telzo2000/cool942tb/case_design/stl/magent_bottomcase/cool942tb_magnet_right_bottomcase.step

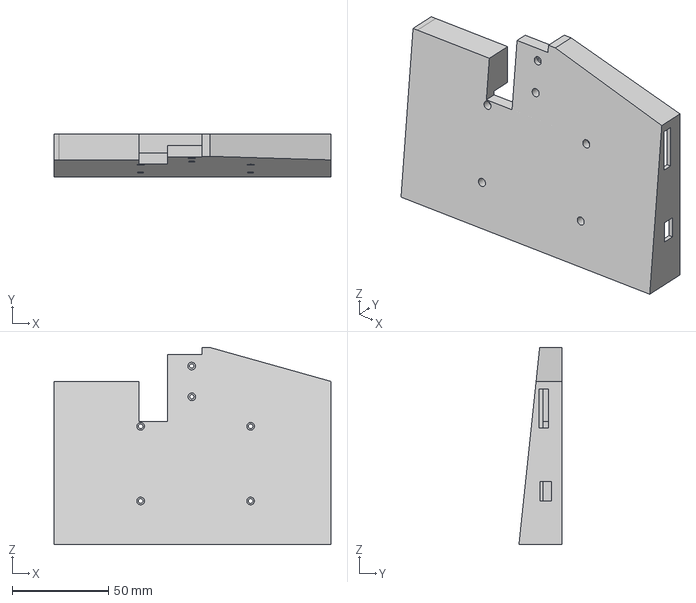
[picture p18: CAD file, 2025-01-30]
case_design/stl/magent_bottomcase/cool942tb_magnet_right_bottomcase.step
144.0 x 22.4 x 102.4 mm
