telzo2000/cool942tb/case_design/stl/with_battery_bottomcase/cool942tb_right_with_battery_bottomcase_6mm.stl

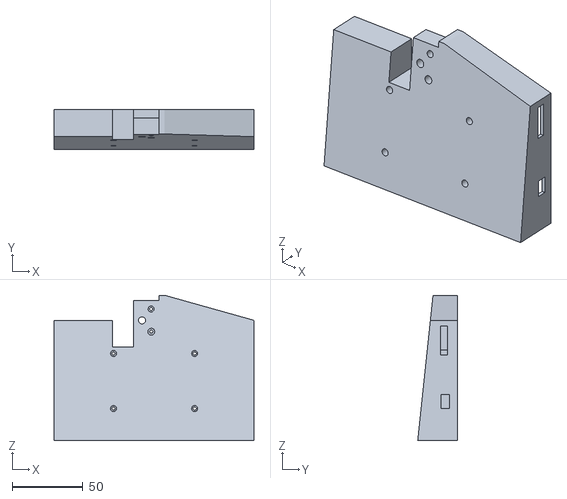
[picture p19: CAD file, 2025-02-10]
case_design/stl/with_battery_bottomcase/cool942tb_right_with_battery_bottomcase_6mm.stl
140.8 x 27.9 x 102.4
