telzo2000/cool942tb/case_design/stl/with_Battery_bottomcase_and_magnet/cool942tb_left_with_battery_bottomcase_6mm.stl

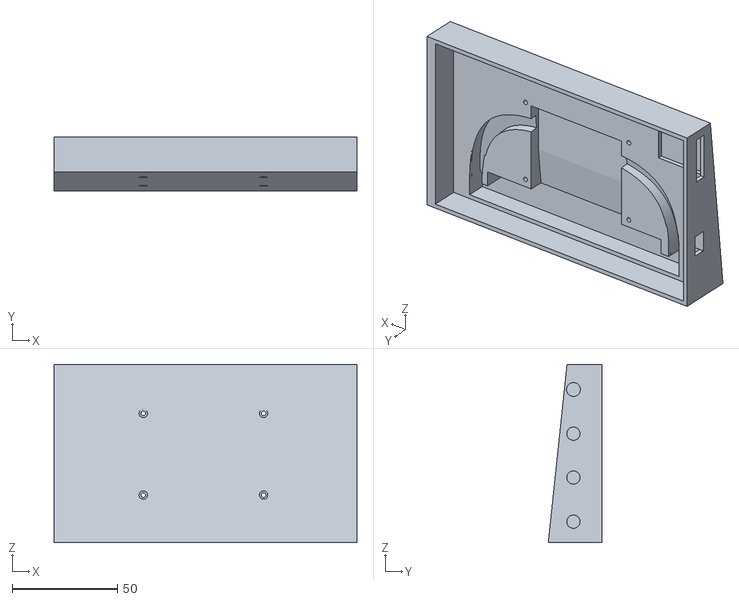
[picture p20: CAD file, 2025-02-21]
case_design/stl/with_Battery_bottomcase_and_magnet/cool942tb_left_with_battery_bottomcase_6mm.stl
144.0 x 25.4 x 84.8
