telzo2000/cool942tb/case_design/stl/ballcase/cool942tb_trackball_case_type_a.stl

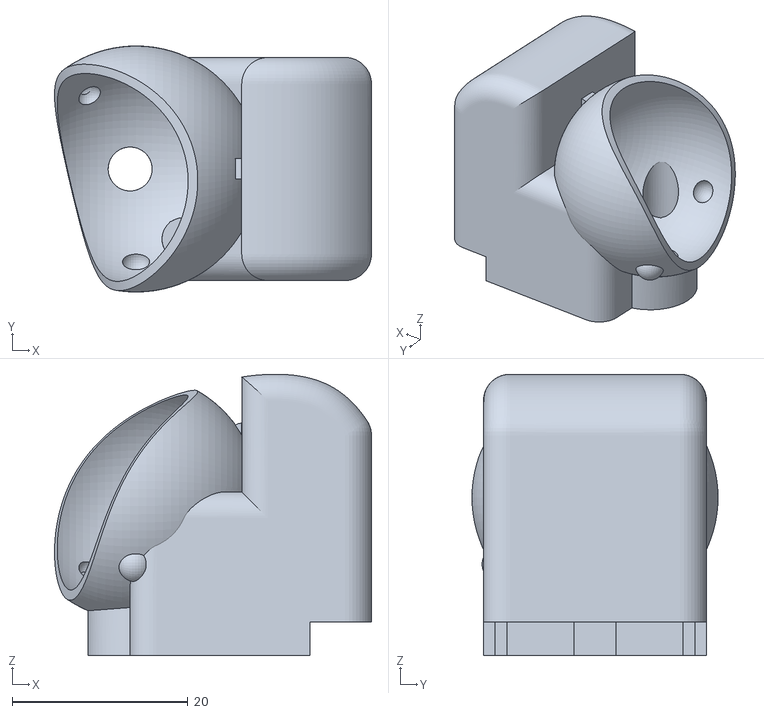
[picture p21: CAD file, 2025-02-01]
case_design/stl/ballcase/cool942tb_trackball_case_type_a.stl
36.1 x 28.0 x 32.0
