telzo2000/cool942tb/case_design/stl/with_Battery_bottomcase_and_magnet/cool942tb_right_with_battery_bottomcase.stl

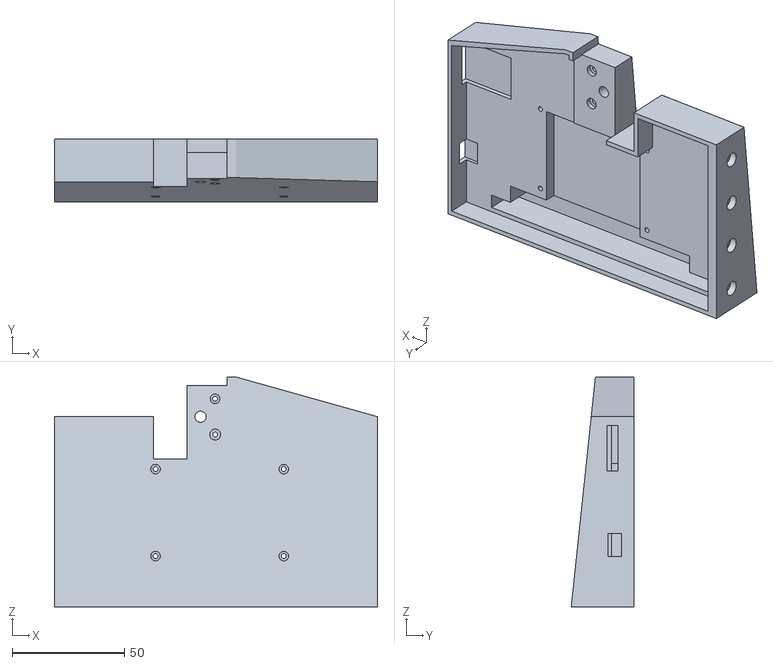
[picture p23: CAD file, 2025-02-08]
case_design/stl/with_Battery_bottomcase_and_magnet/cool942tb_right_with_battery_bottomcase.stl
143.9 x 27.9 x 102.4
